Arich-Hardware/PCB/hardware/documents/Zynq-Video-Board-v1.2-Schematic.pdf

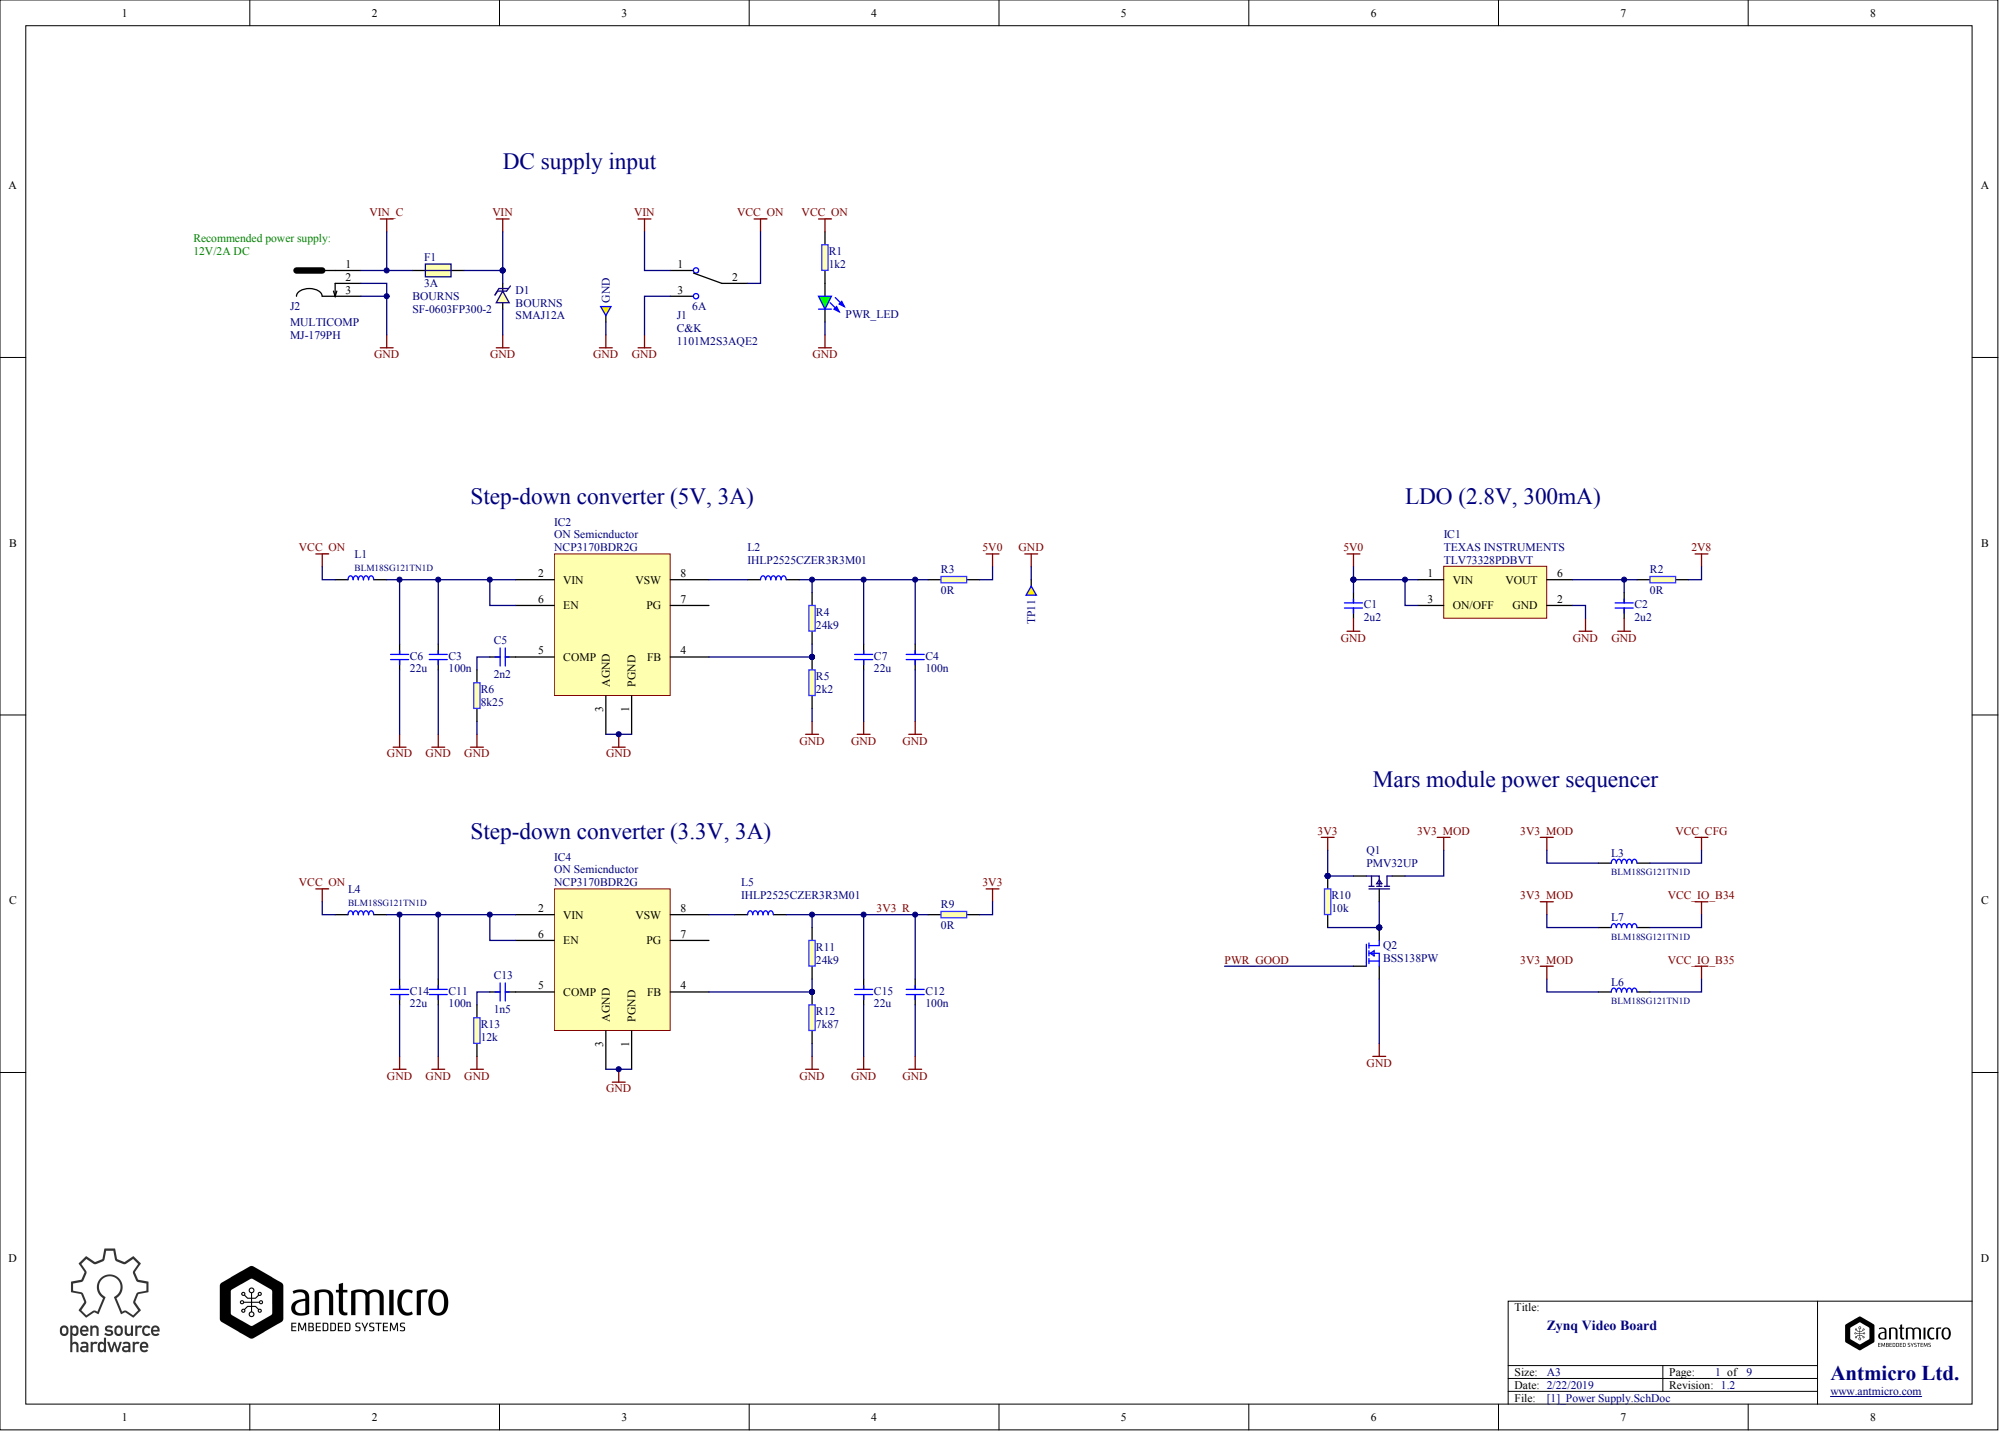
[picture p18: page 1]

Mars module power sequencer

Title: Zynq Video Board | Antmicro Ltd. www.antmicro.com

Size: A3 | Page: 1 of 9
Date: 2/22/2019 | Revision: 1.2

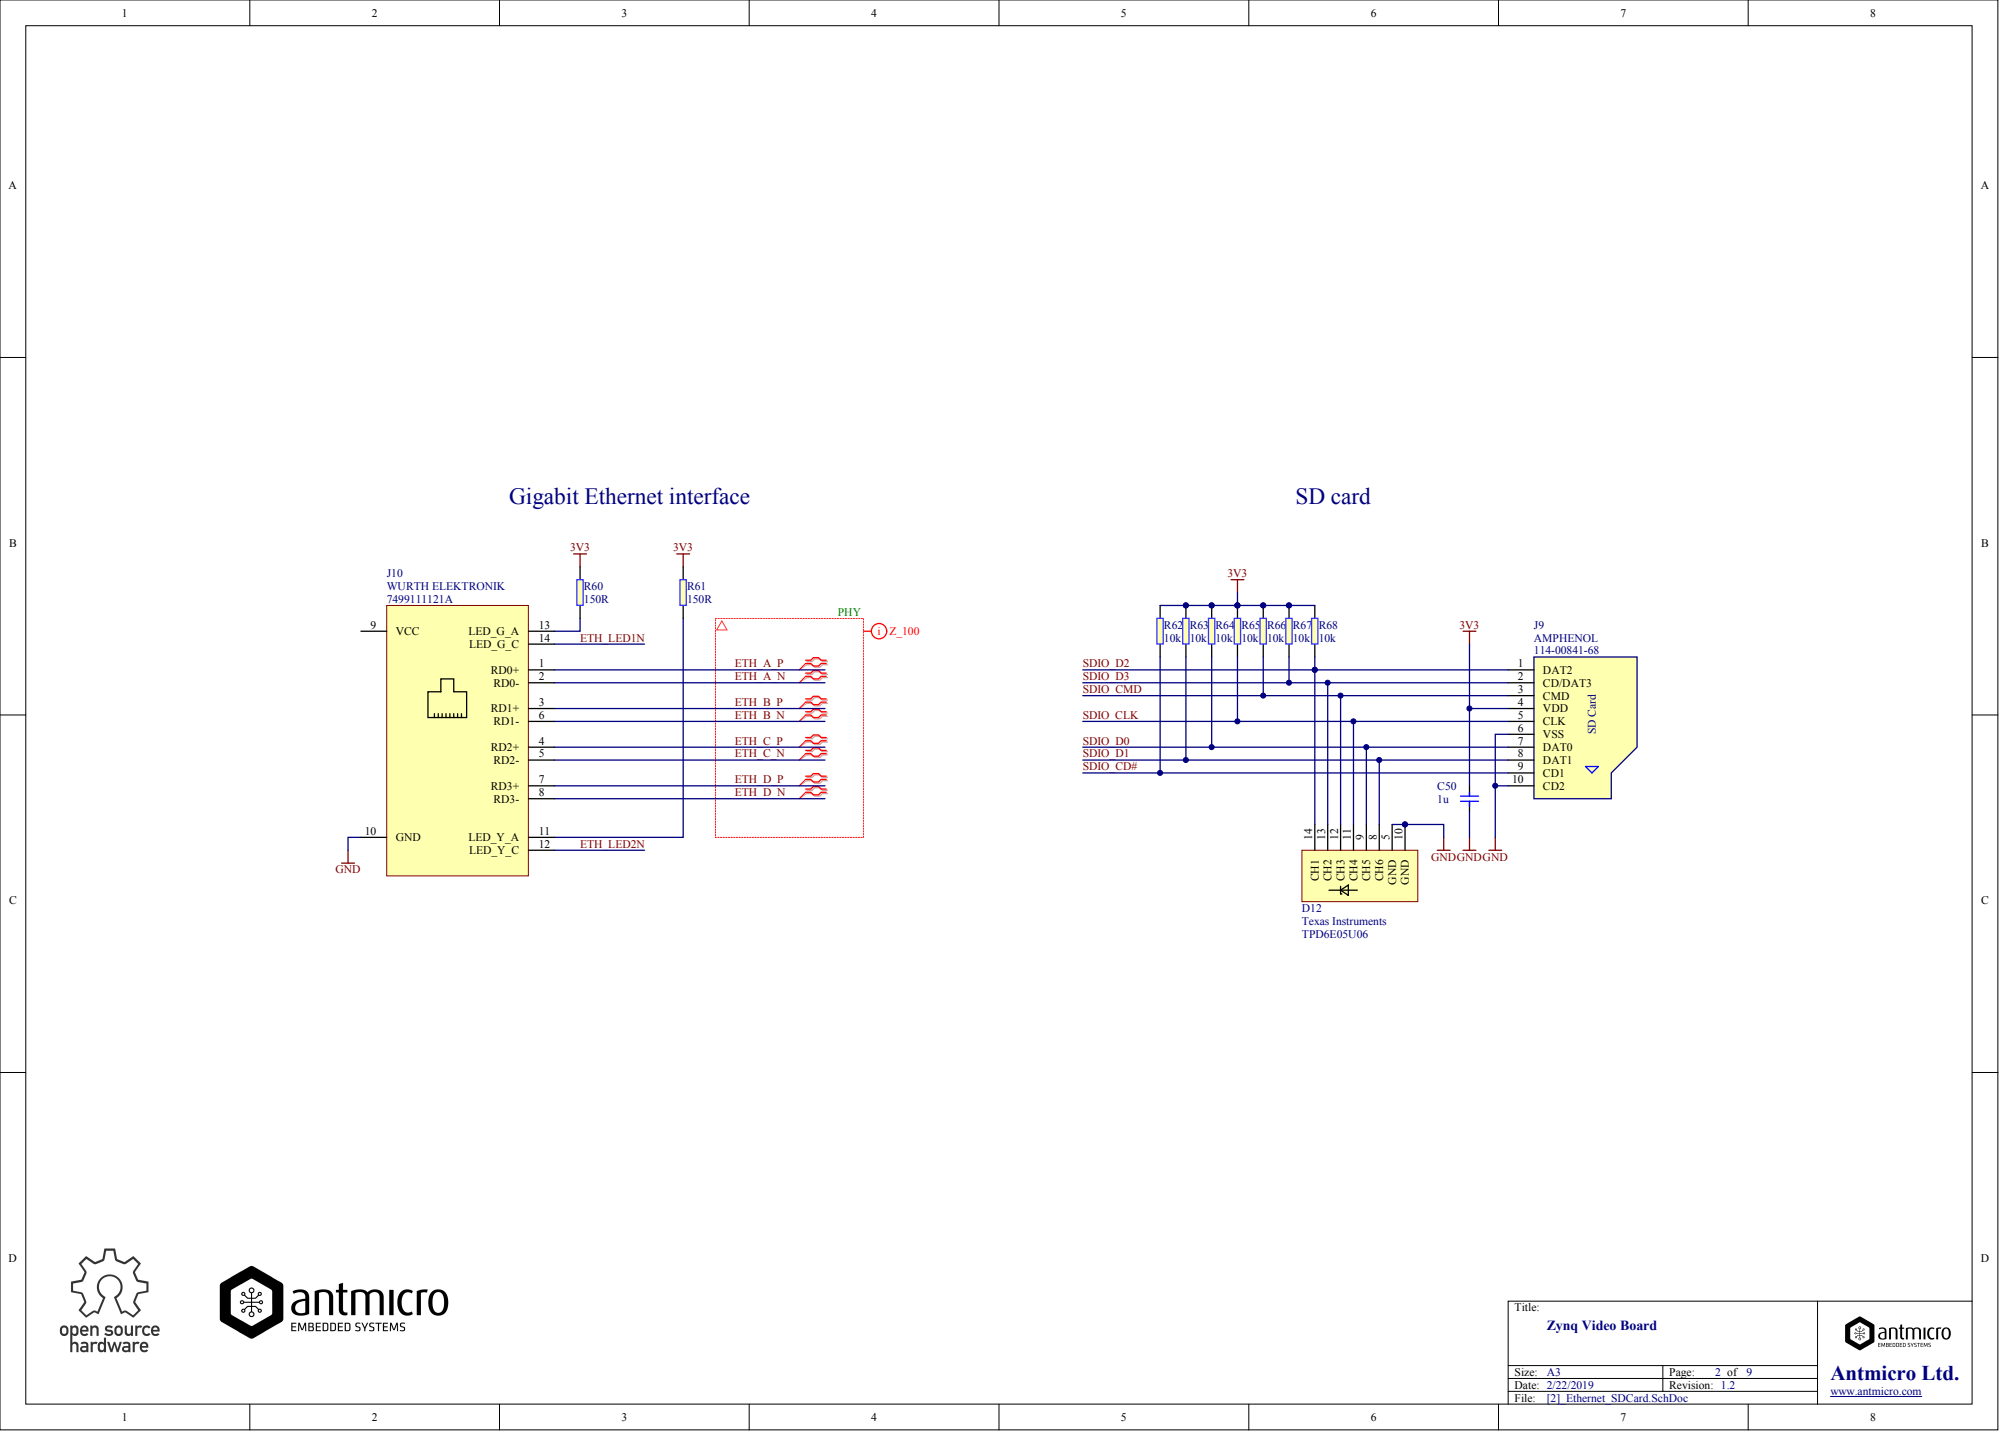
[picture p19: page 2]

Antmicro Ltd. www.antmicro.com

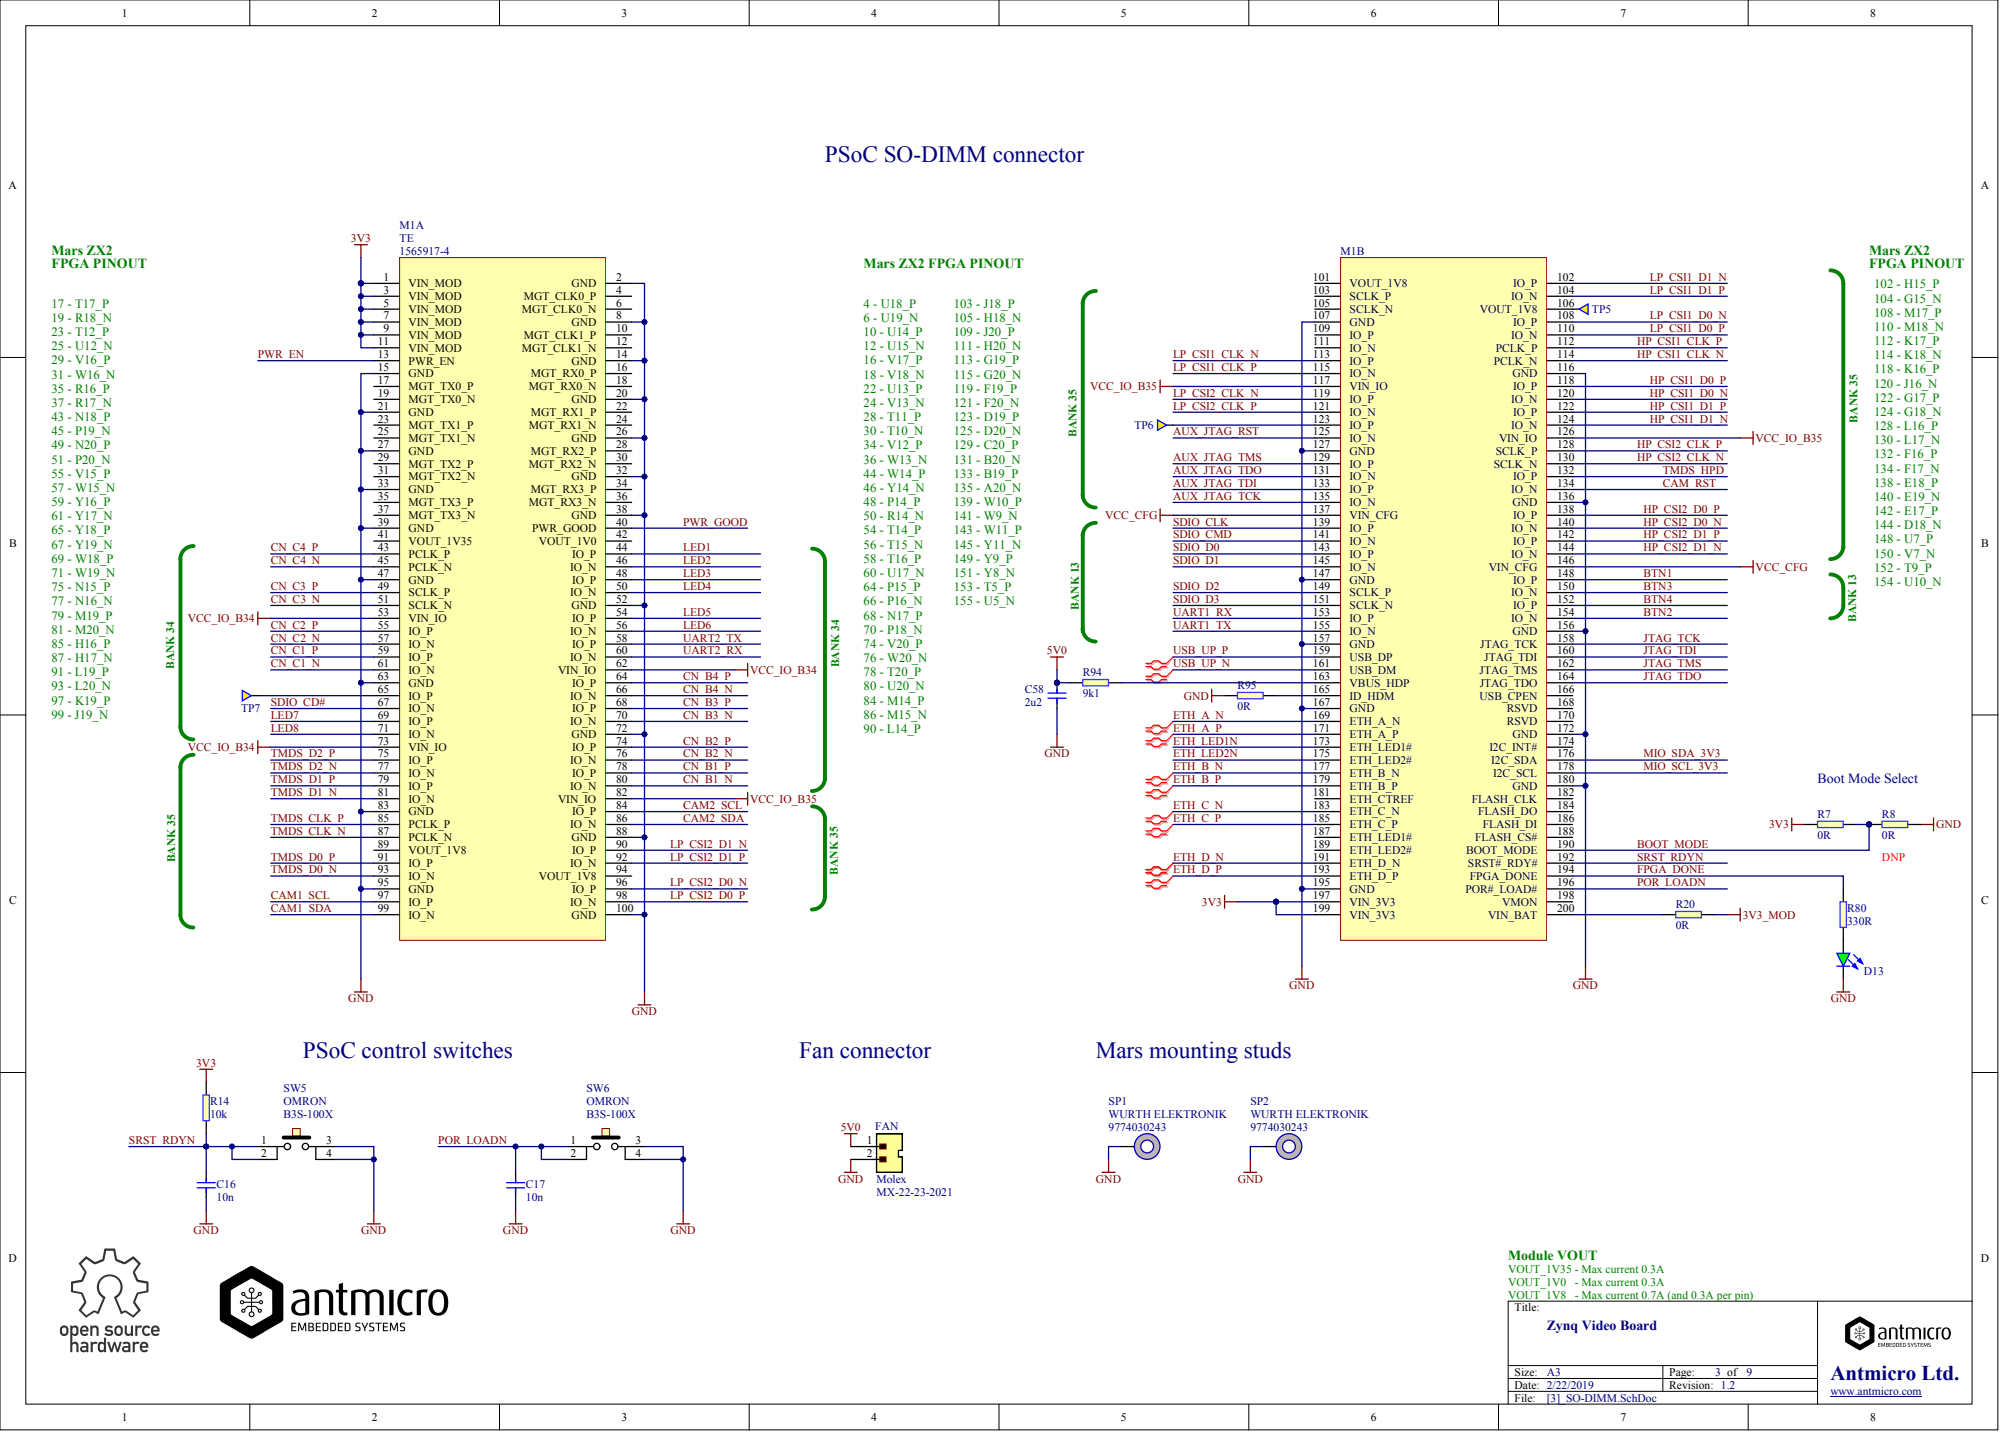
[picture p20: page 3]

PSoC SO-DIMM connector

USB_DP 159 USB_DM 161 VBUS_HDP 163 ID_HDM 165

GND 63 IO_P 65 IO_N 67 IO_P 69 IO_N 71 | CN_B4_N

GND 83 | CN_B2_N

CN_B1_P
CN_B1_N

PCLK_P 85 PCLK_N 87

BOOT_MODE

Module VOUT
VOUT_1V35 - Max current 0.3A
VOUT_1V0 - Max current 0.3A
VOUT_1V8 - Max current 0.7A (and 0.3A per pin)

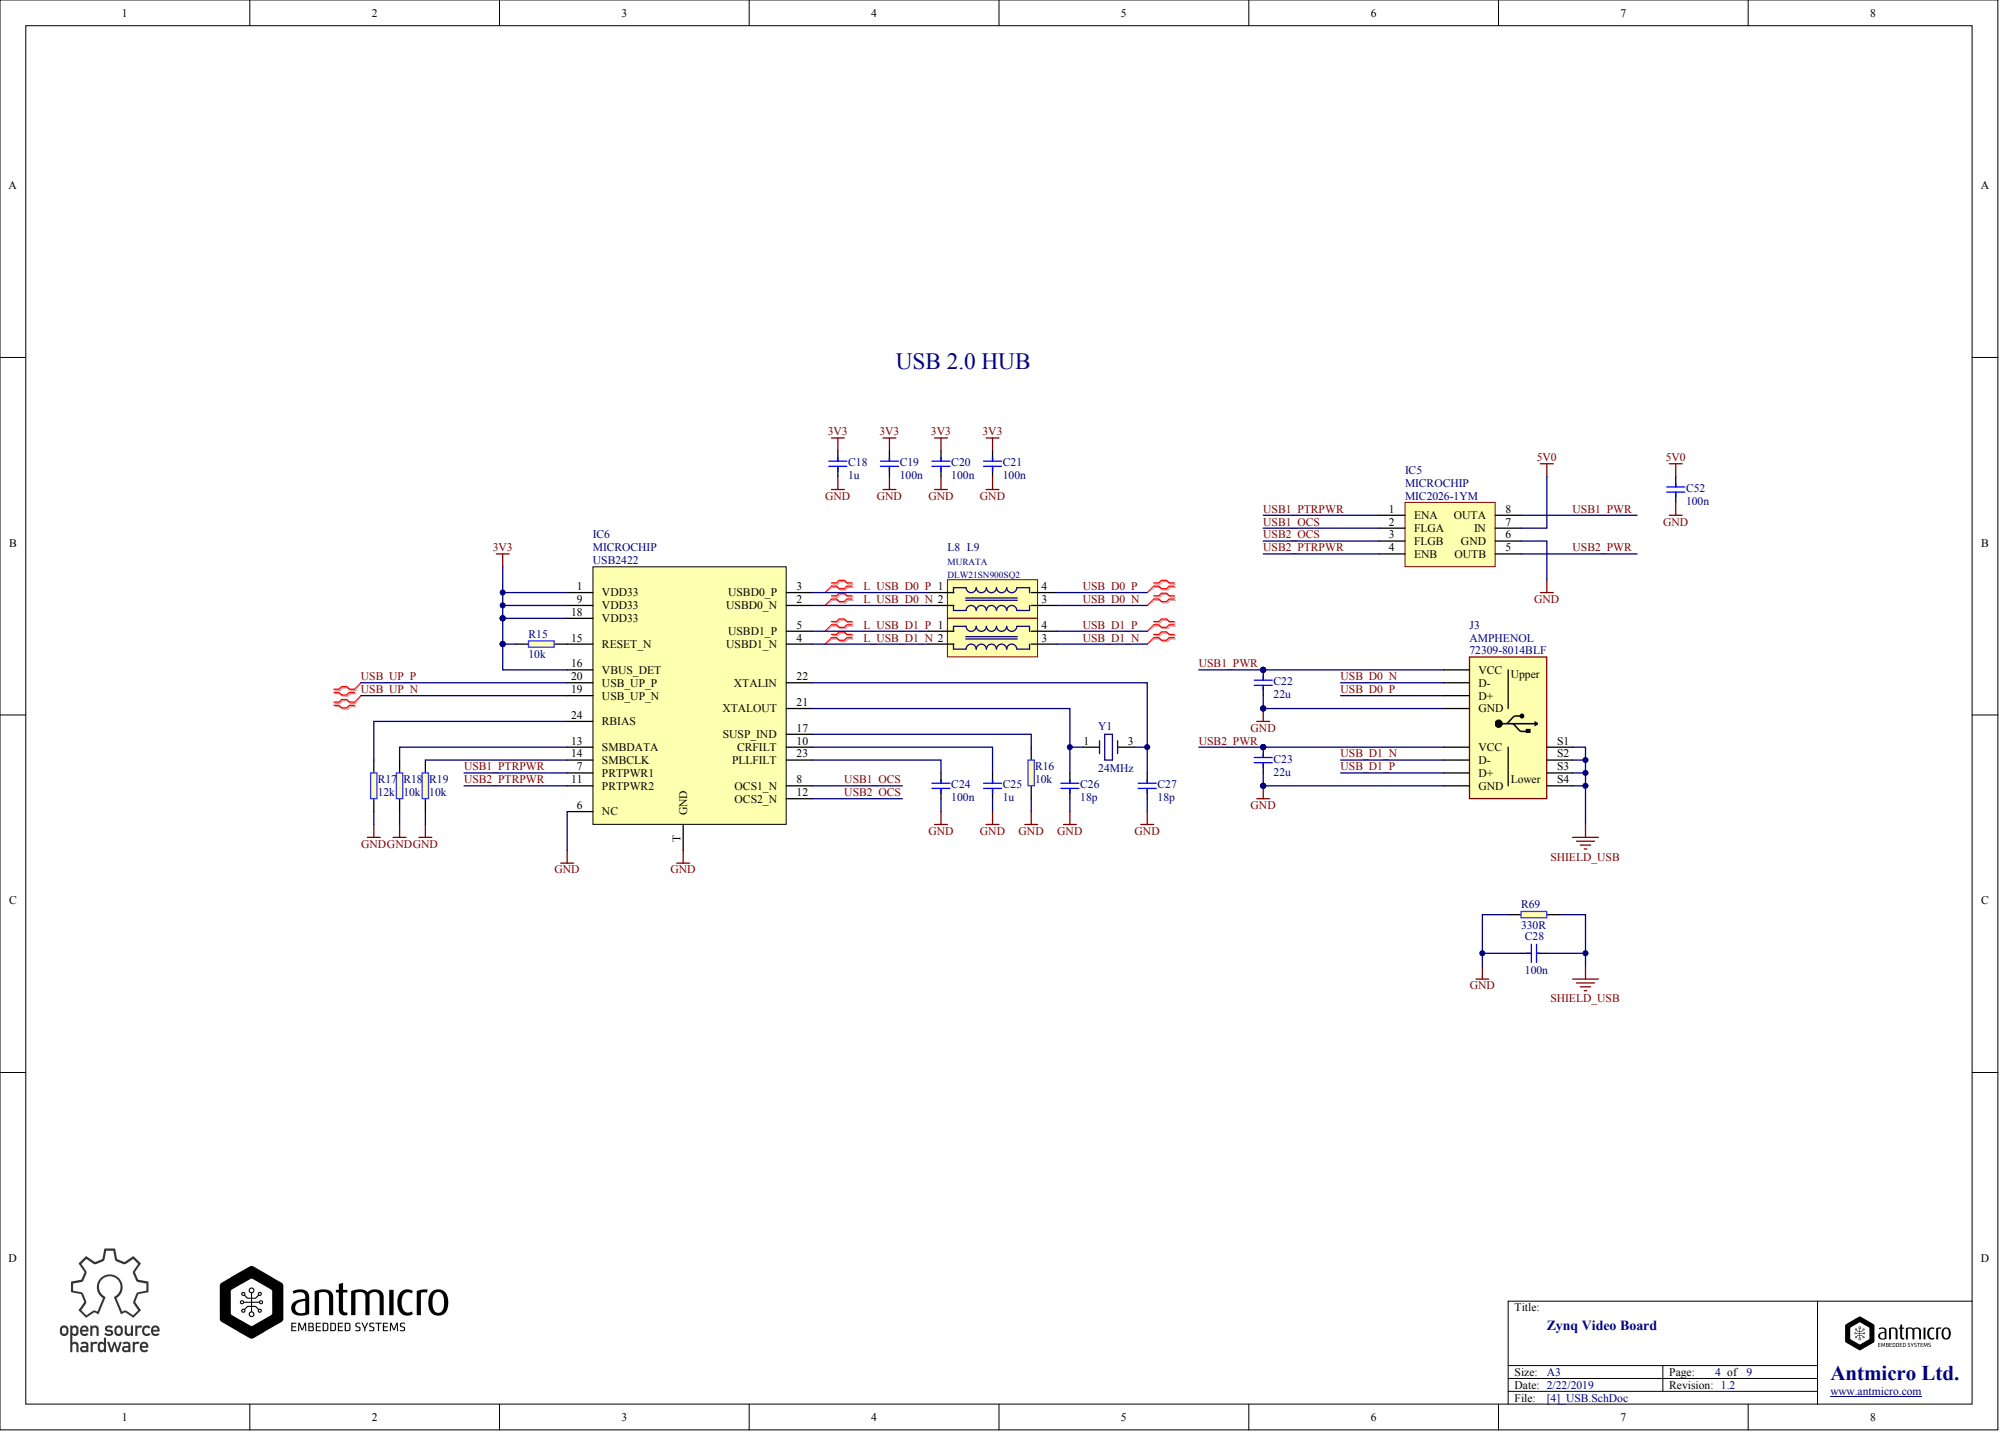
[picture p21: page 4]

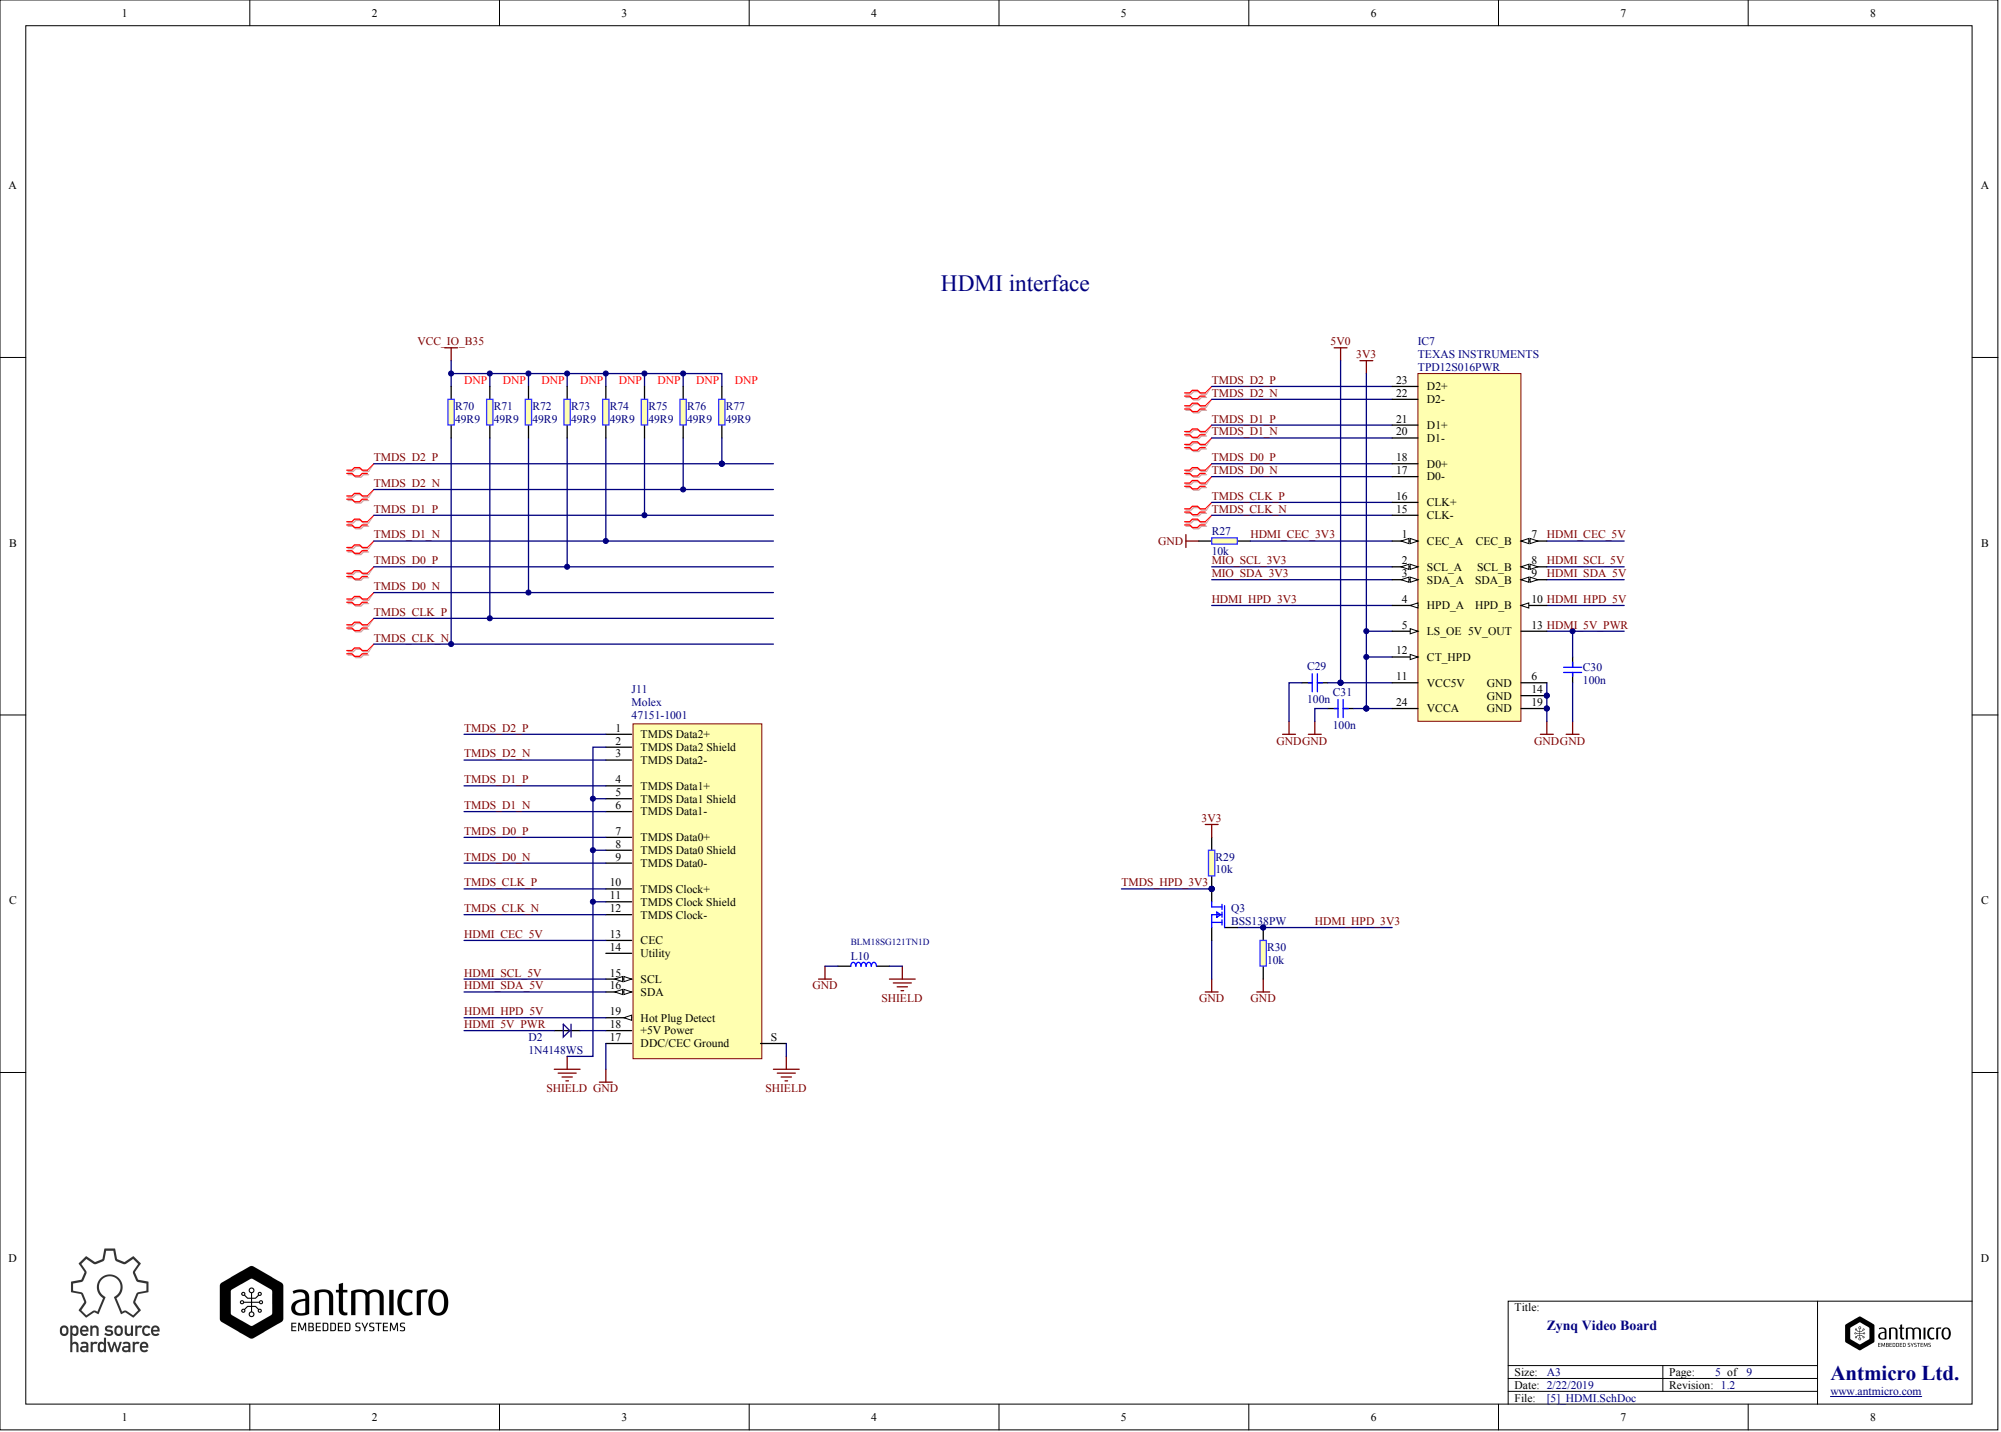
[picture p22: page 5]

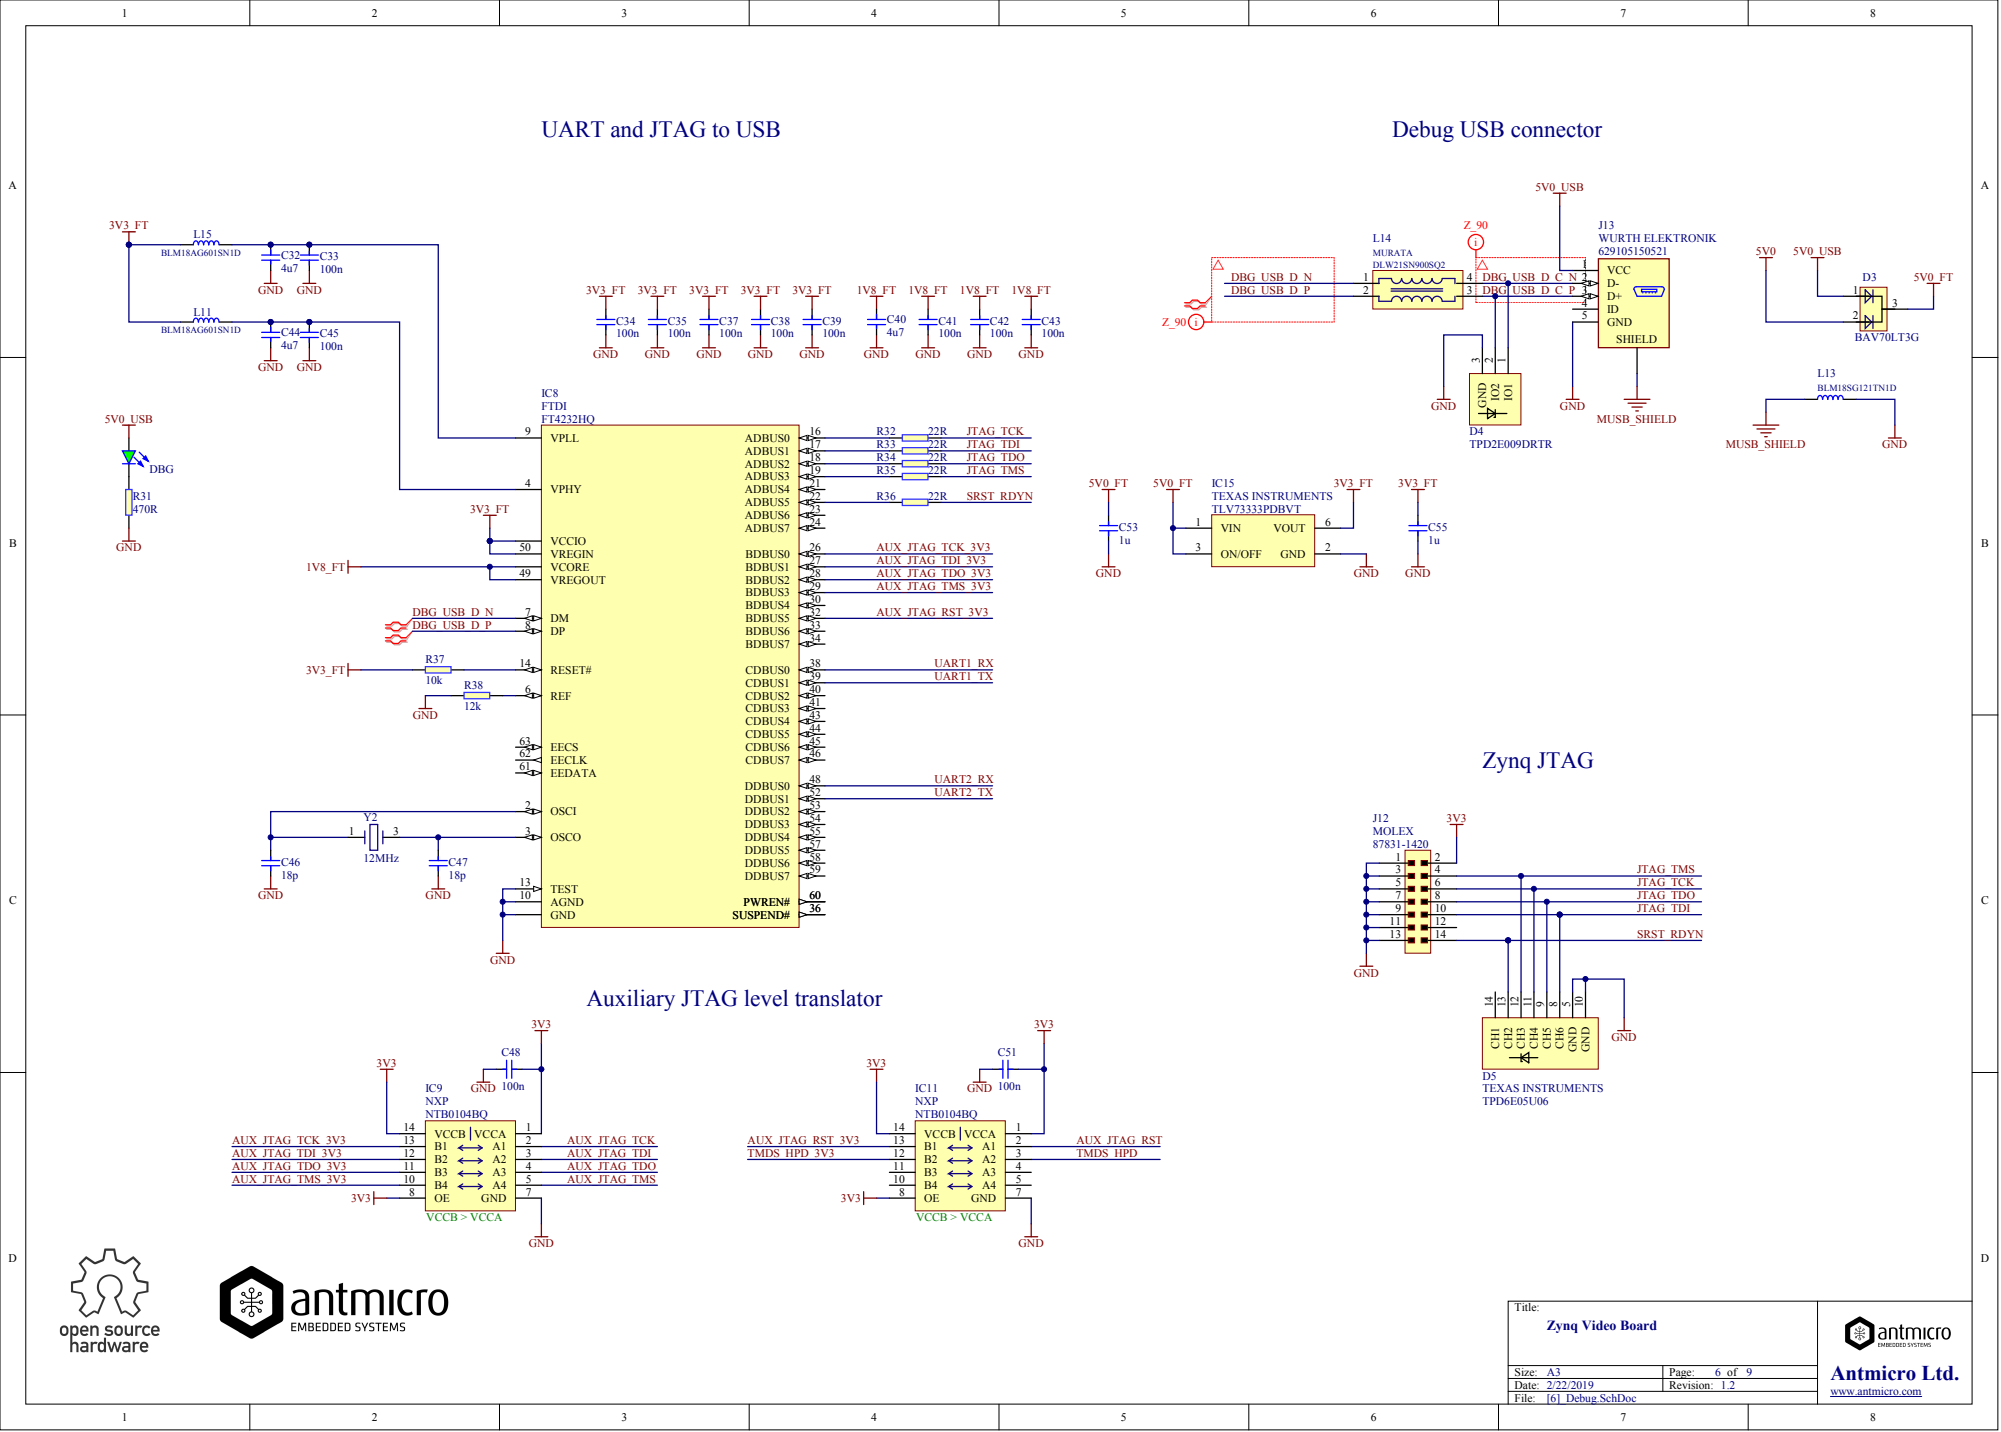
[picture p23: page 6]

UART and JTAG to USB

VPHY 4

VREGIN 50

ON/OFF 3

Auxiliary JTAG level translator

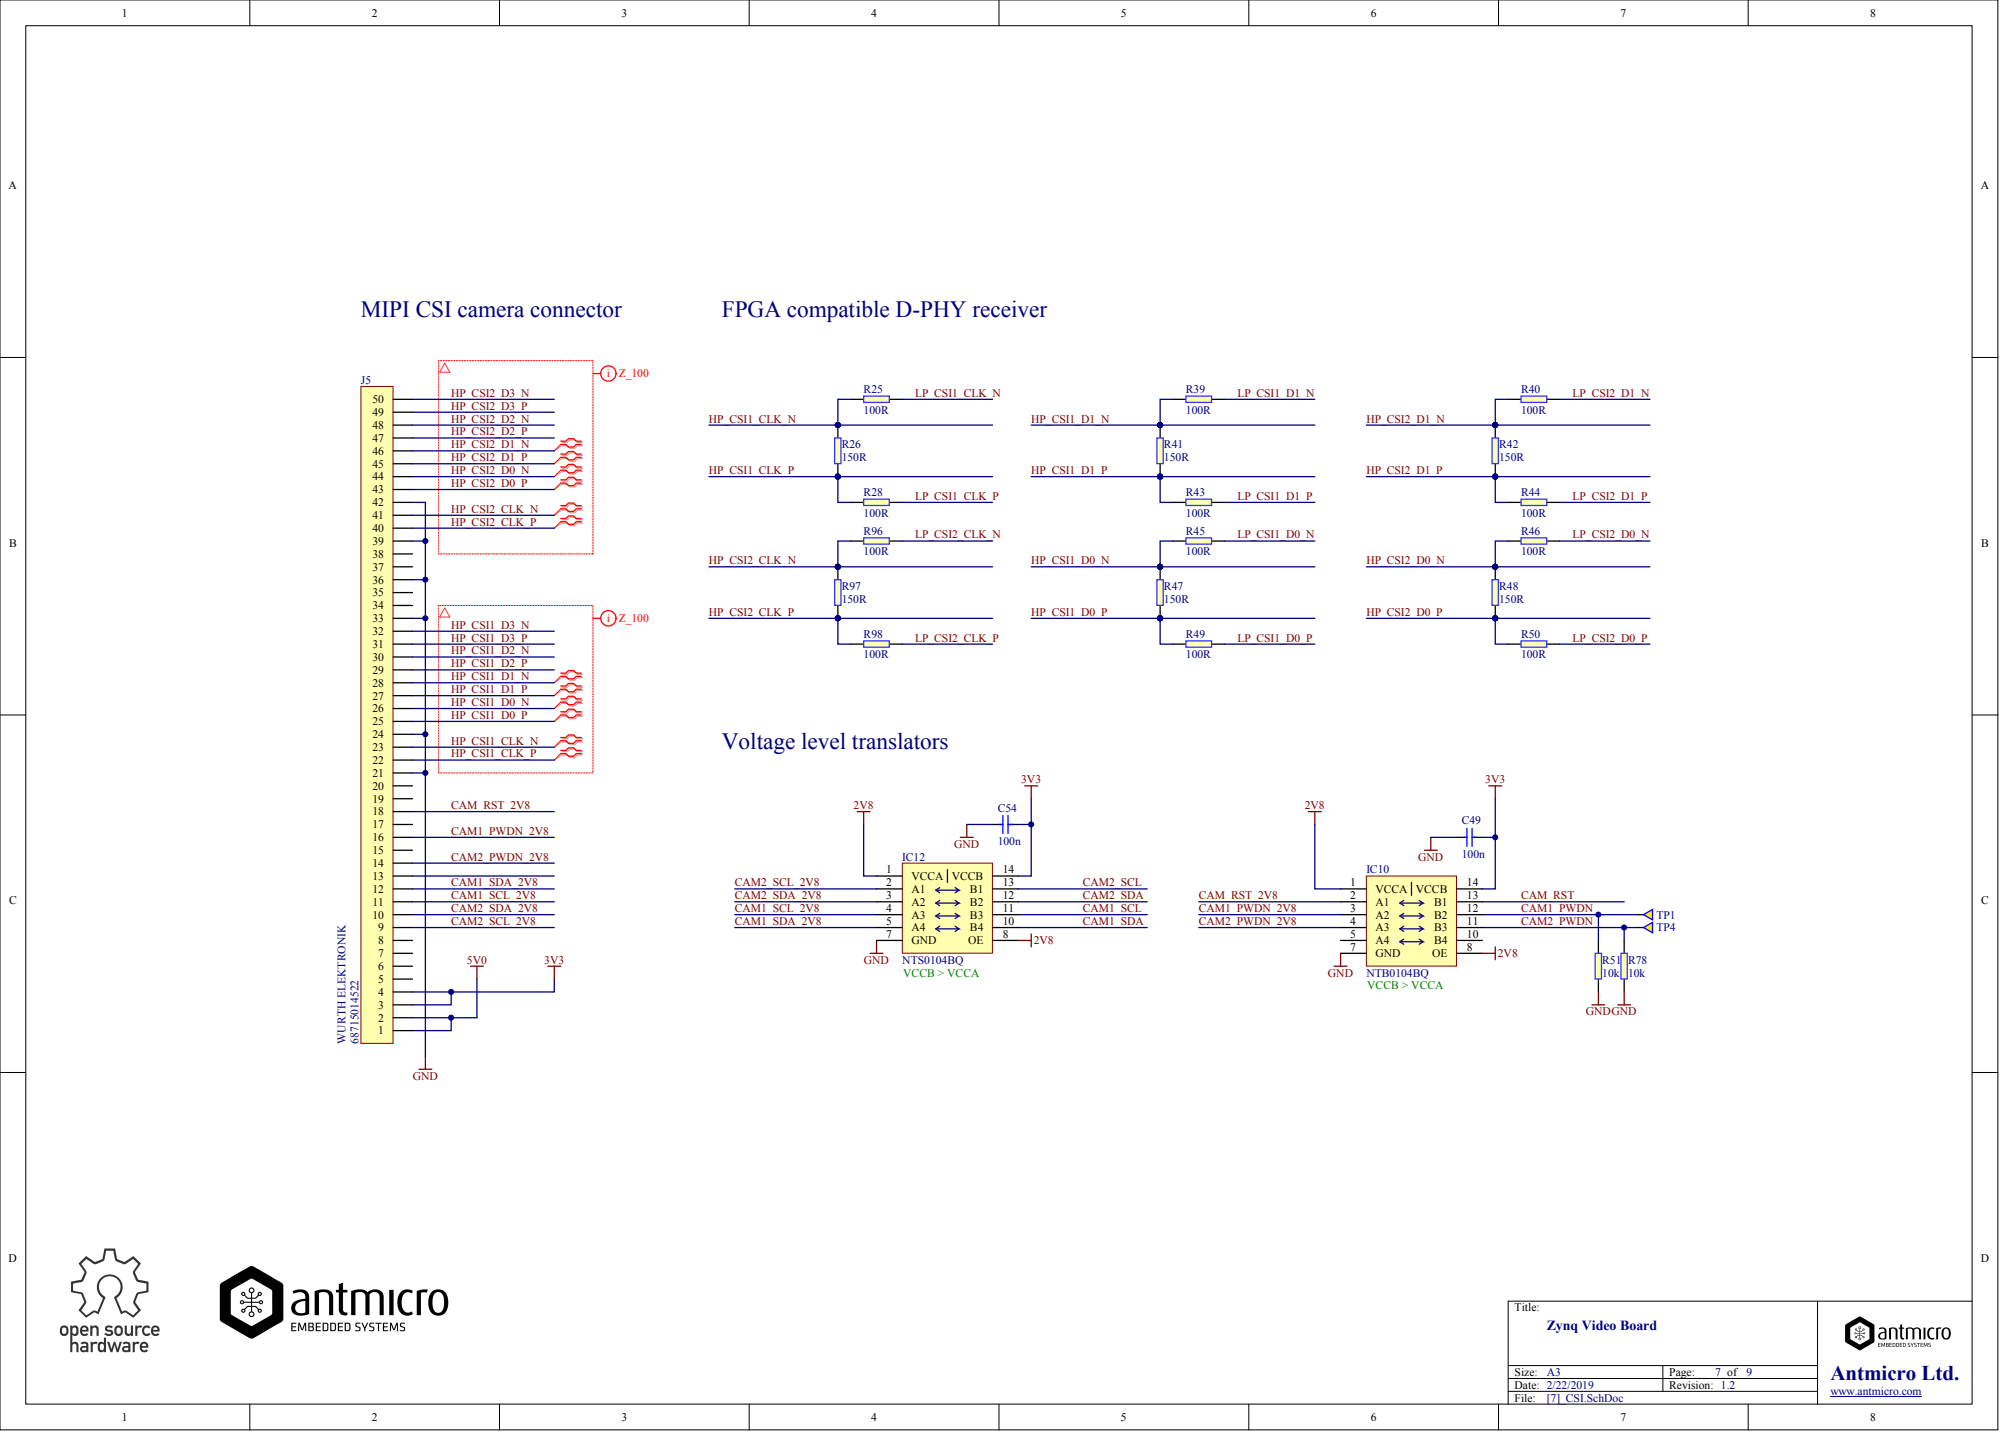
[picture p24: page 7]

MIPI CSI camera connector

FPGA compatible D-PHY receiver
LP_CSI1_CLK_P LP_CSI1_CLK_N LP_CSI2_CLK_P LP_CSI2_CLK_N

HP_CSI1_D3_P
HP_CSI1_D2_N
HP_CSI1_D2_P
HP_CSI1_D1_N
HP_CSI1_D1_P
HP_CSI1_D0_N
HP_CSI1_D0_P

HP_CSI1_CLK_N
HP_CSI1_CLK_P

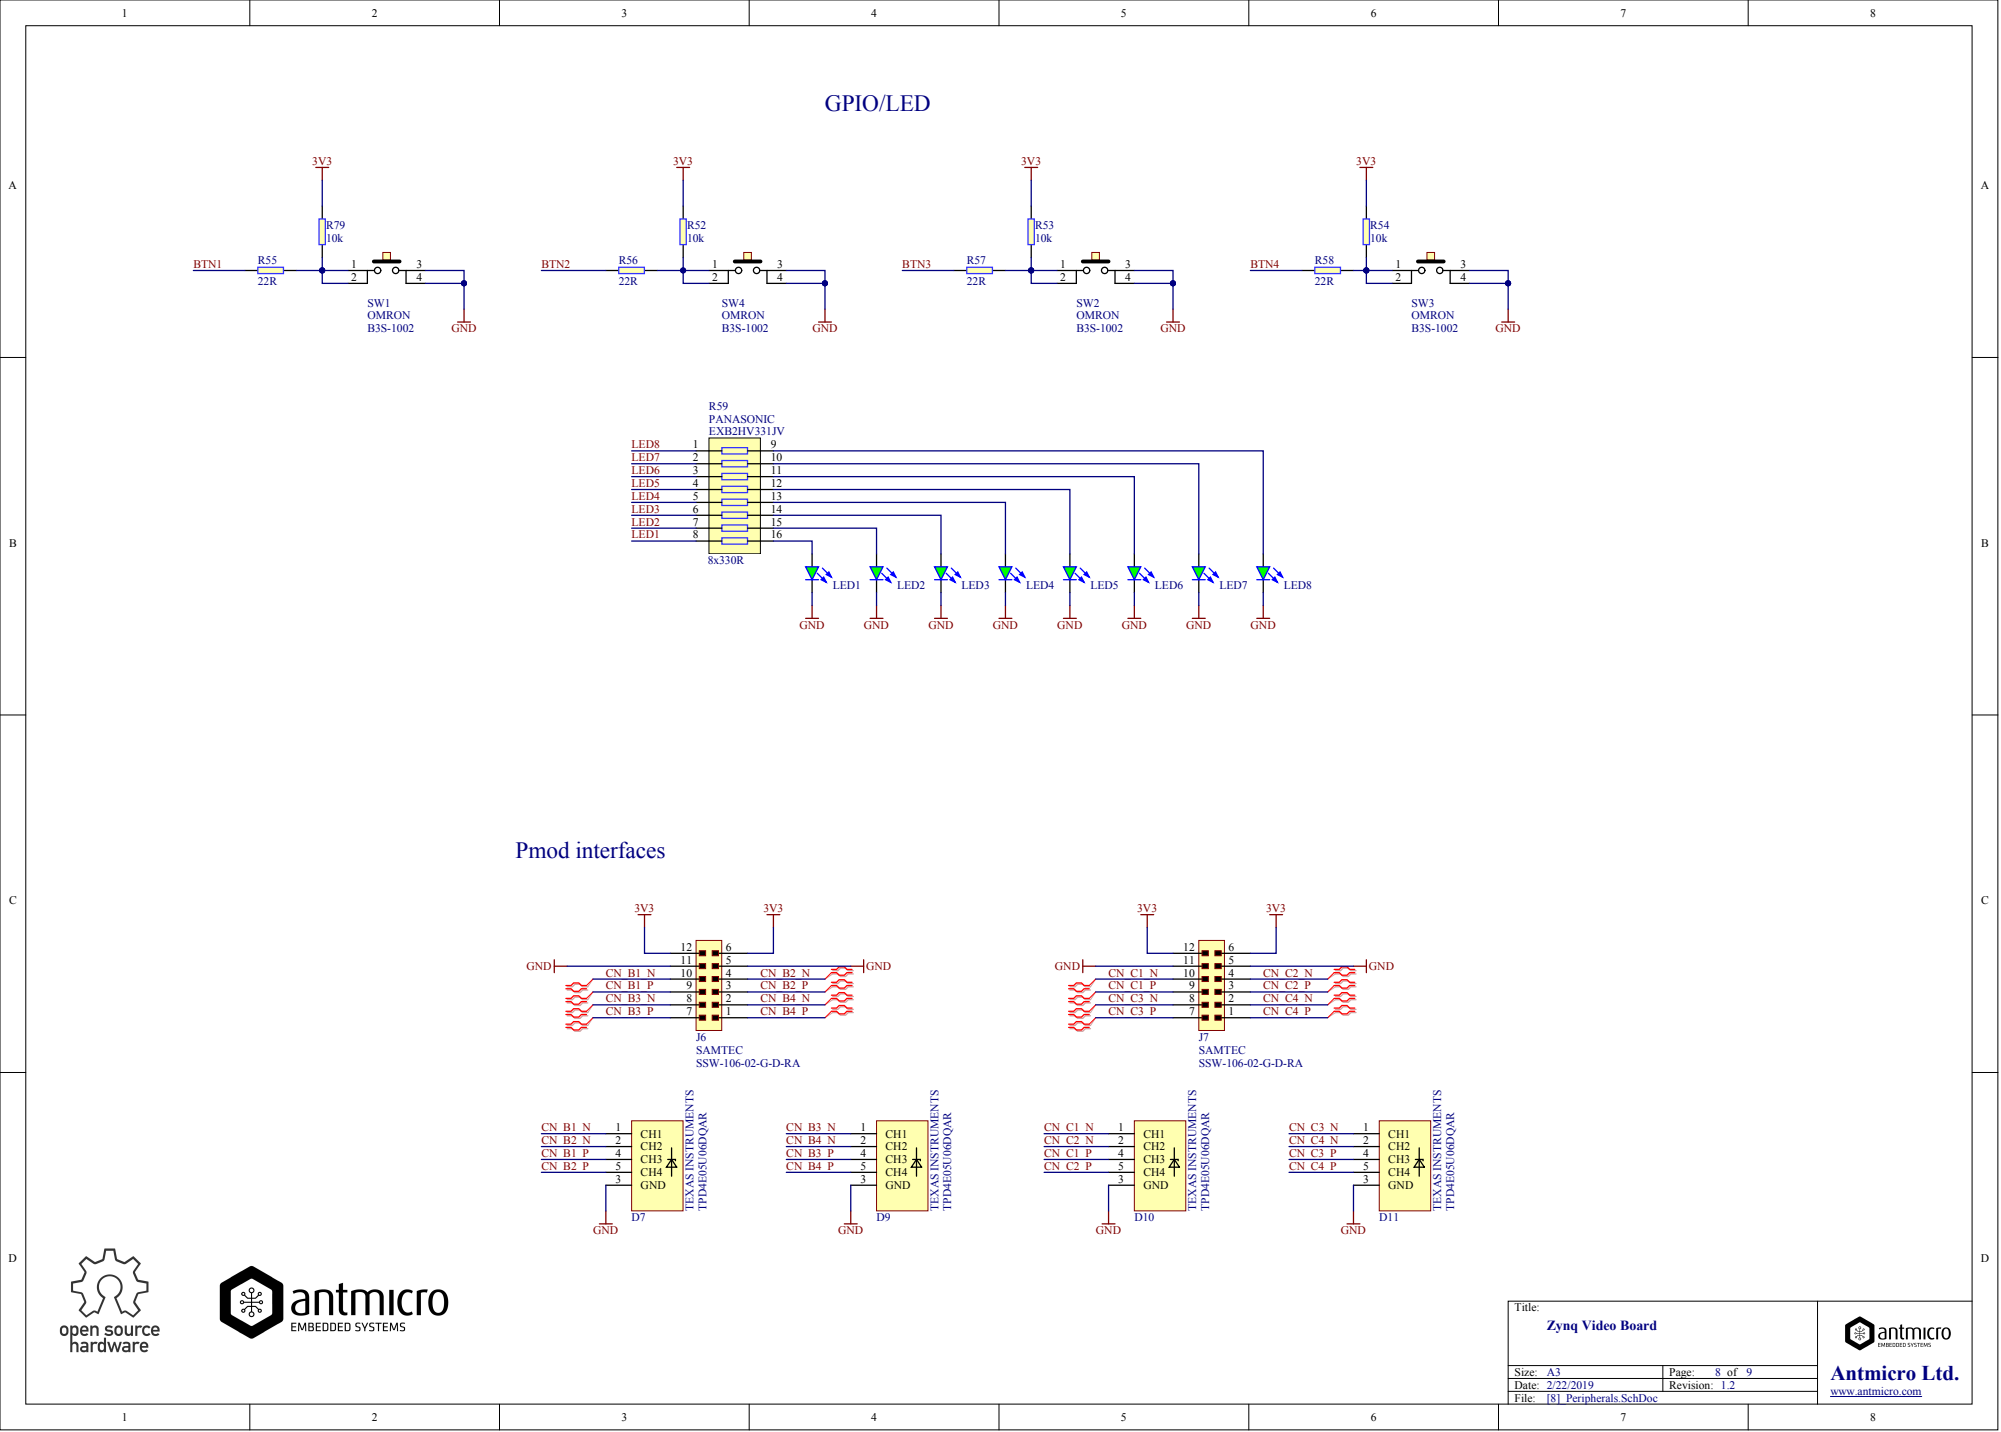
[picture p25: page 8]

10
11
12
13
14
15
16

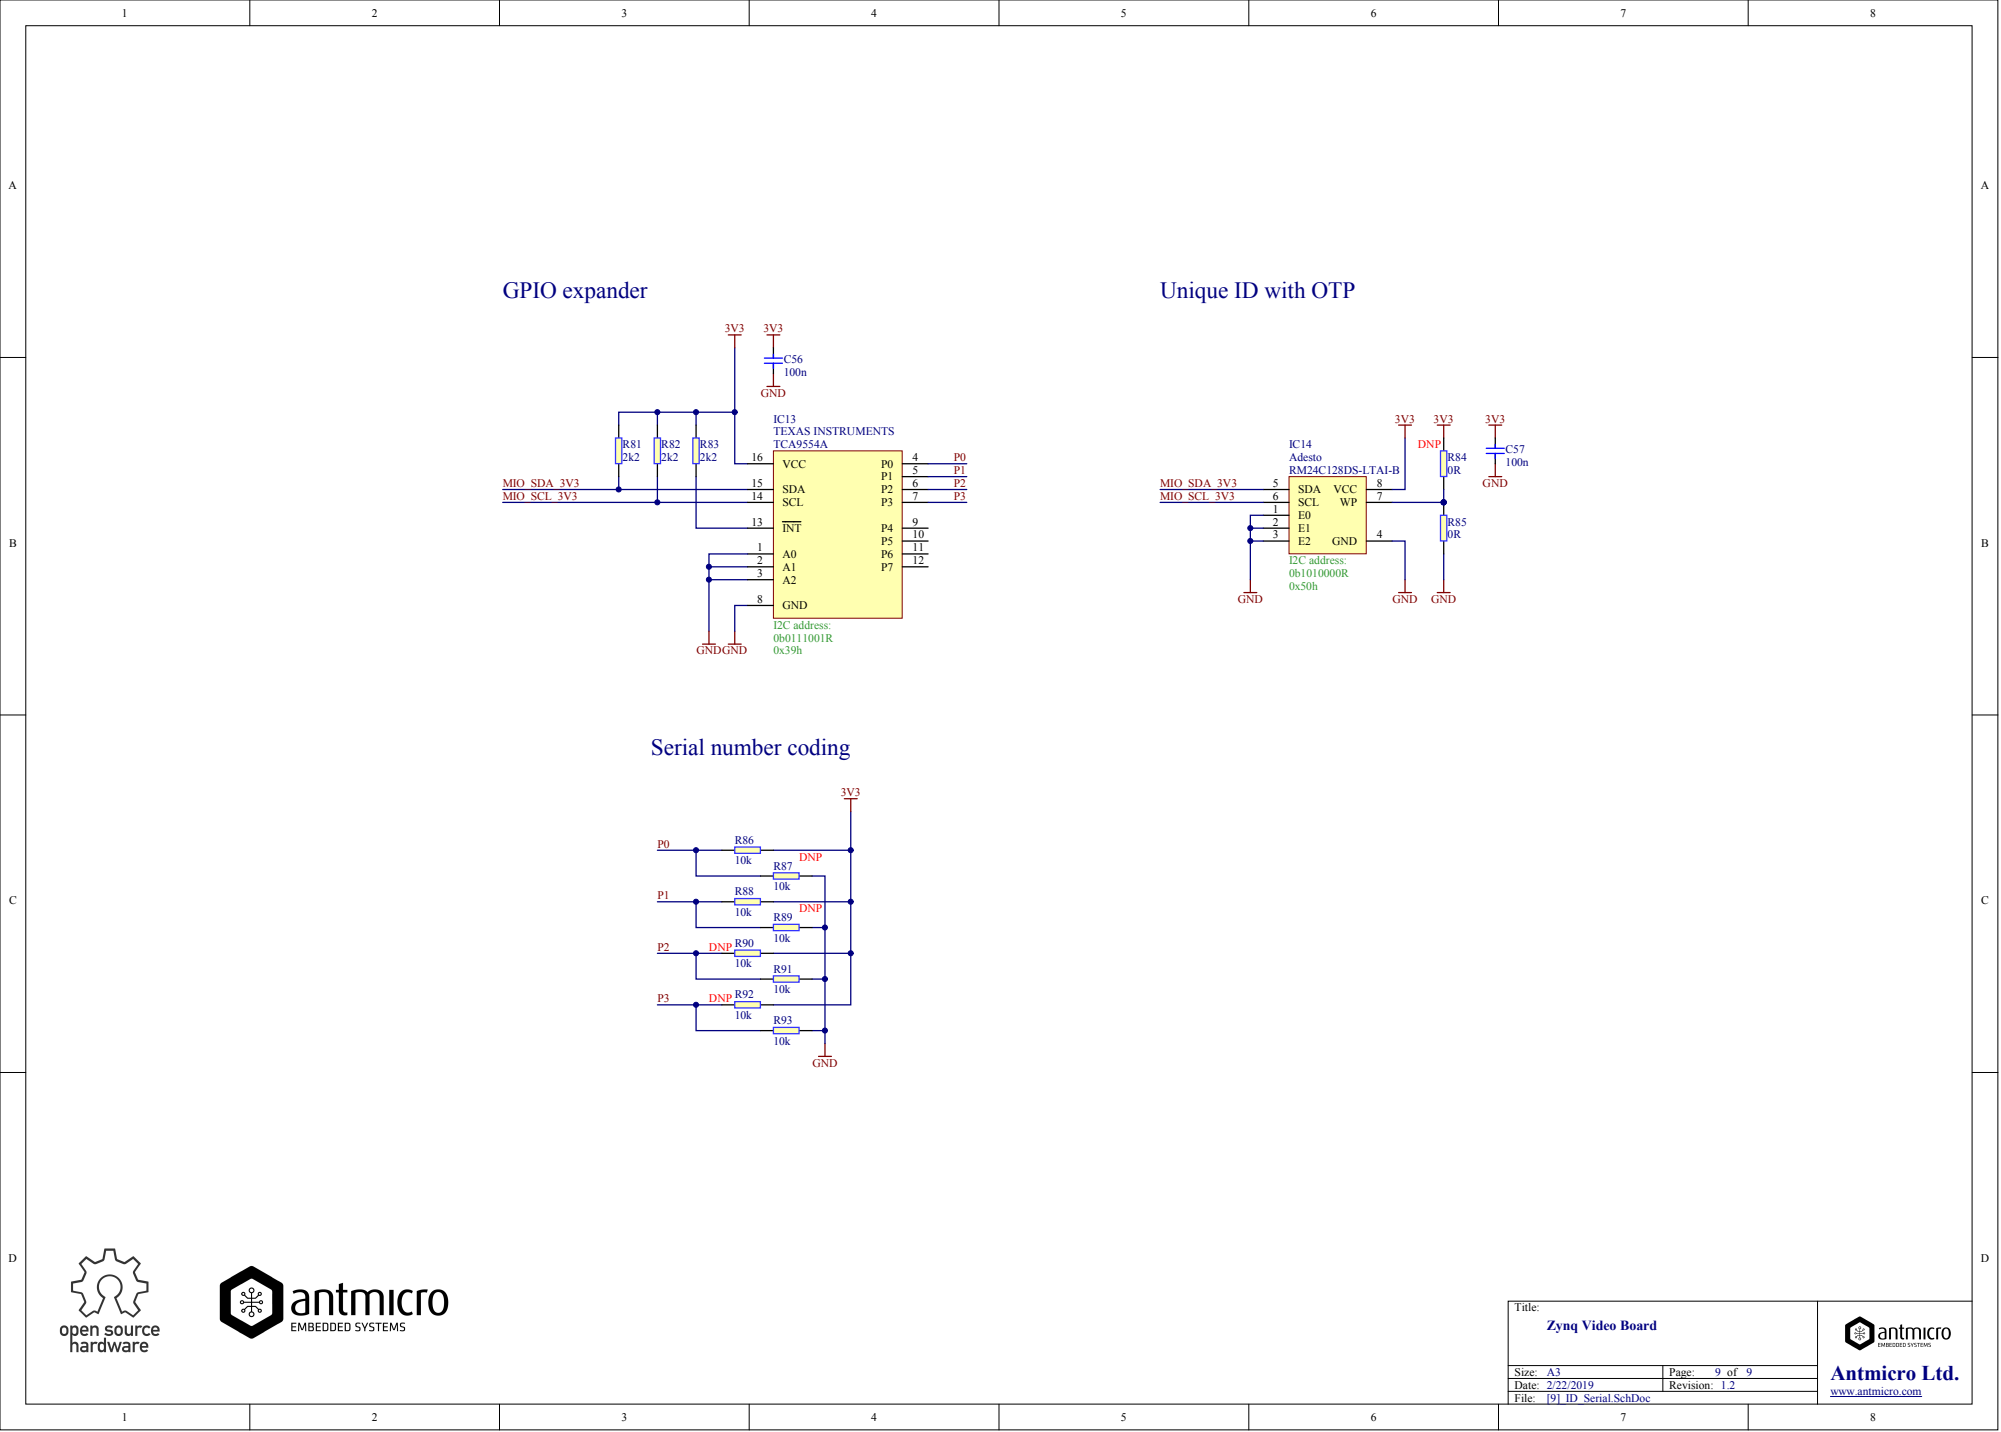
[picture p26: page 9]

Unique ID with OTP

INT 13
