Arich-Hardware/PCB/hardware/siPM_Board/SiPM_Board.pdf

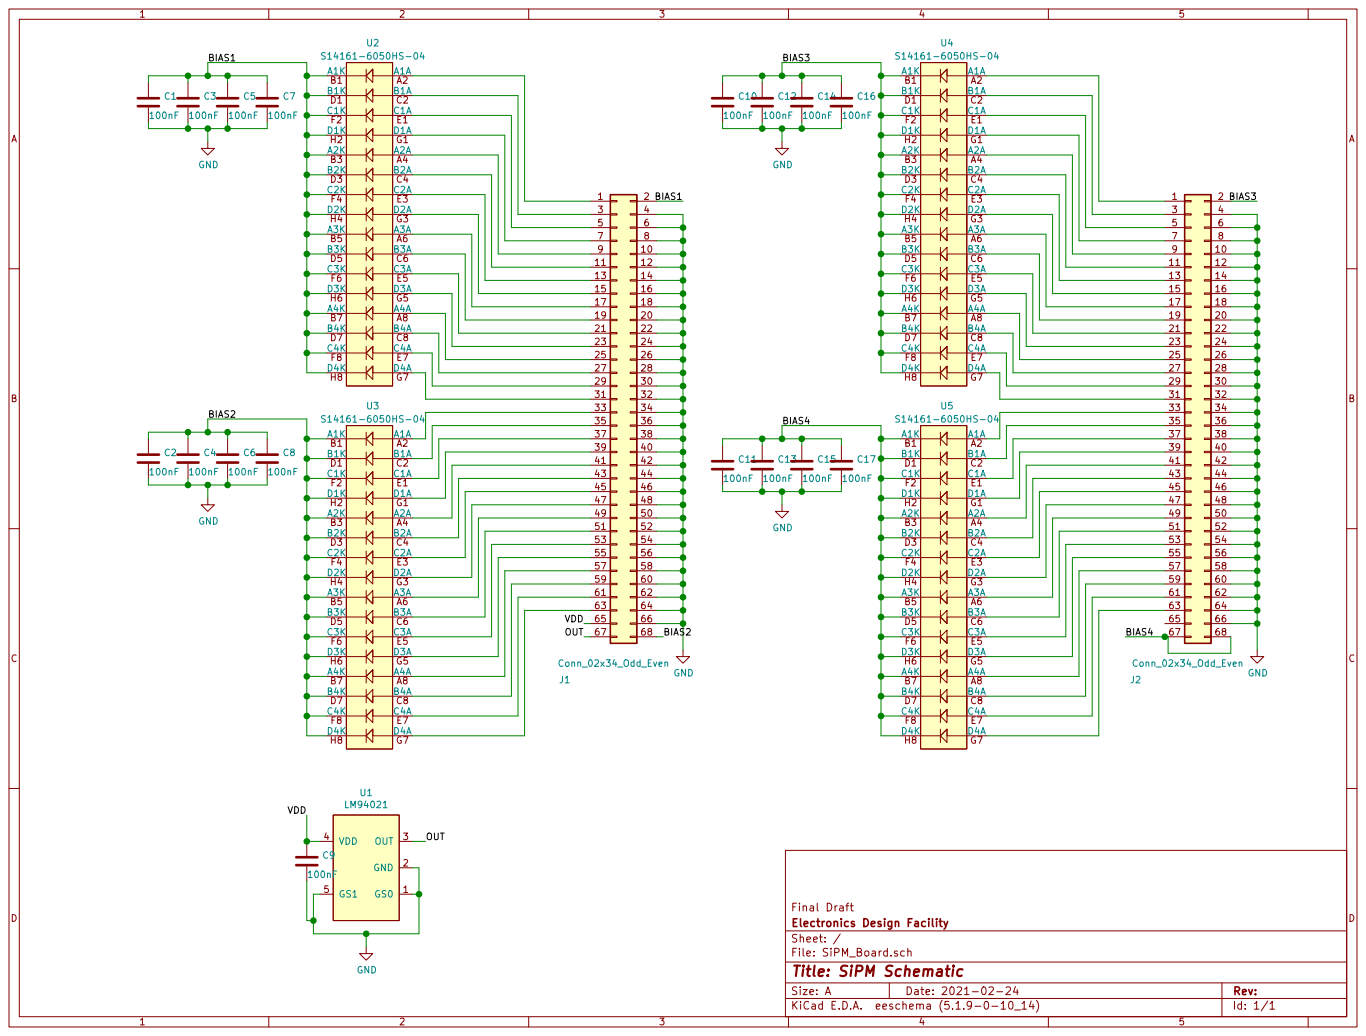
[picture p27: page 1]

55 | 56 | 55 | 56
57 | 58 | 57 | 58

File: SiPM_Board.sch Sheet: / Electronics Design Facility Final Draft

Id: 1/1 Title: SiPM Schematic
